jrcohen/SmartStepp/Images/test2.JPG

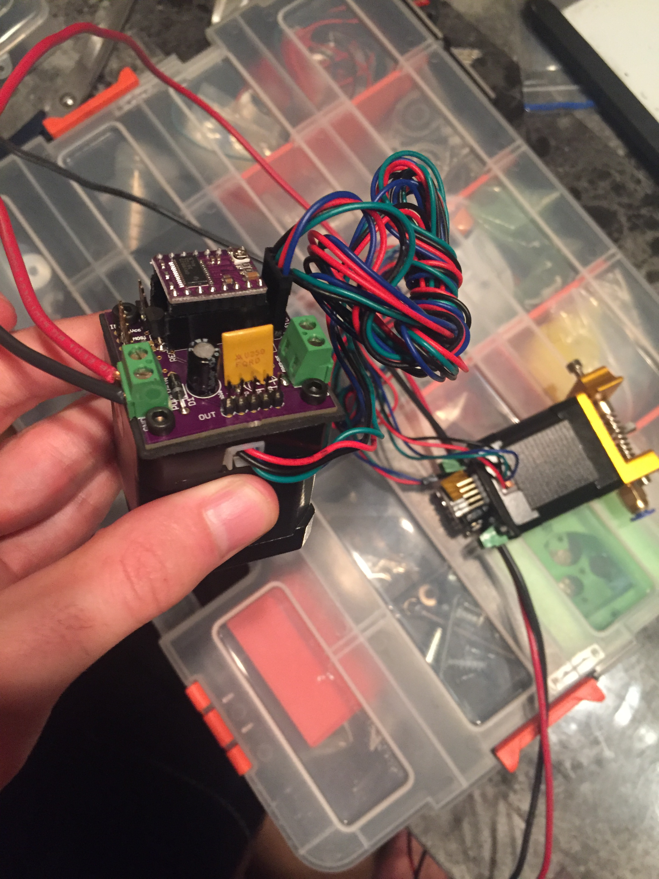
Images/test2.JPG
