jrcohen/SmartStepp/Smartstep/TableData.h

#ifndef __TABLEDATA_H__
#define __TABLEDATA_H__

#include "Arduino.h"


extern const float table1[];
extern const float table2[];
extern const float table3[];


// Add additional tables for each extra motor controlled by this arduino board

#endif
